UlisesGascon/Calidad-del-Aire/caja/caja_3d_trasera.png

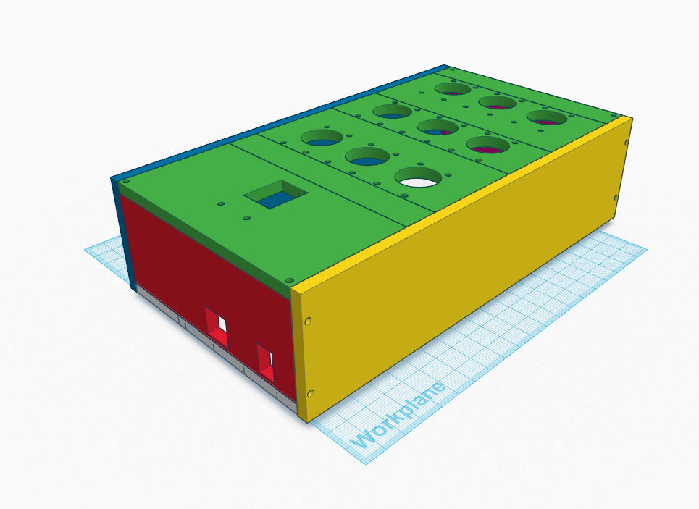
caja/caja_3d_trasera.png
