UlisesGascon/Calidad-del-Aire/snippets/mq-3/mq-3_alcohol.ino

/*
PARTIENDO DE  http://www.naylampmechatronics.com/blog/42_Tutorial-sensores-de-gas-MQ2-MQ3-MQ7-y-MQ13.html
*/

int pin_mq = 12;

void setup() {
  Serial.begin(9600);
  pinMode(pin_mq, INPUT);
}

void loop() {

  // Valores Analógicos
  int adc_MQ = analogRead(A12); //Lemos la salida analógica  del MQ
  float voltaje = adc_MQ * (5.0 / 1023.0); //Convertimos la lectura en un valor de voltaje
  float Rs=1000*((5-voltaje)/voltaje);  //Calculamos Rs con un RL de 1k
  double alcohol=0.4091*pow(Rs/5463, -1.497); // calculamos la concentración  de alcohol con la ecuación obtenida.
  
  // Interruptor
  boolean mq_estado = digitalRead(pin_mq);//Leemos el sensor
  if(mq_estado) //si la salida del sensor es 1
  {
    Serial.println("Sin presencia de alcohol");
  }
  else //si la salida del sensor es 0
  {
    Serial.println("Alcohol detectado");
  }
  
  
  //-------Enviamos los valores por el puerto serial------------
  Serial.print("adc:");
  Serial.print(adc_MQ);
  Serial.print("    voltaje:");
  Serial.print(voltaje);
  Serial.print("    Rs:");
  Serial.print(Rs);
  Serial.print("    alcohol:");
  Serial.print(alcohol);
  Serial.println("mg/L");
  delay(500);
}
